holgi-s/pipong/src/sleep.h

//
// Created by Holger on 17.03.2018.
//

#ifndef LEDBAR_SLEEP_H
#define LEDBAR_SLEEP_H

#include <cstdint>

void sleep_s(uint16_t sec);
void sleep_ms(uint16_t ms);
void sleep_us(uint16_t us);

#endif //LEDBAR_SLEEP_H
